robertstrauss/laser-projector/blender-CAD-modeling/laser-diffusion-raytracing/focal-cone-cloud-tight-no-denoise.png

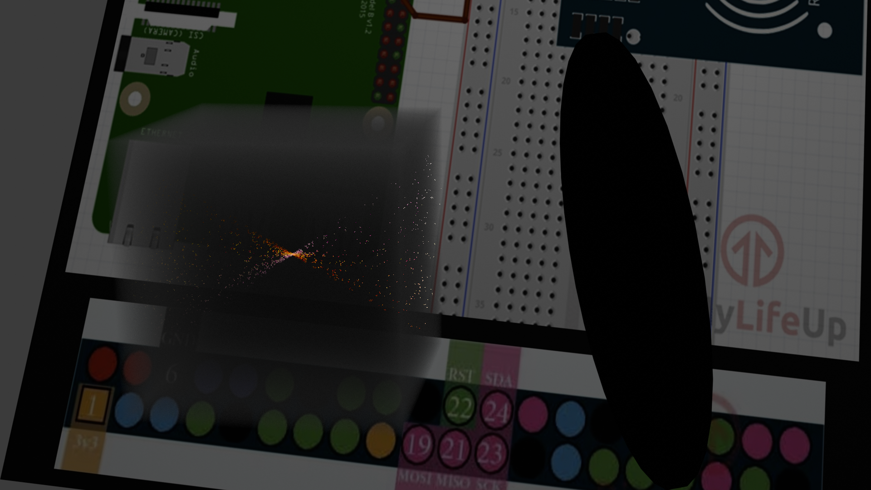
blender-CAD-modeling/laser-diffusion-raytracing/focal-cone-cloud-tight-no-denoise.png
