robertstrauss/laser-projector/blender-CAD-modeling/laser-diffusion-raytracing/focal-cone-cloud.png

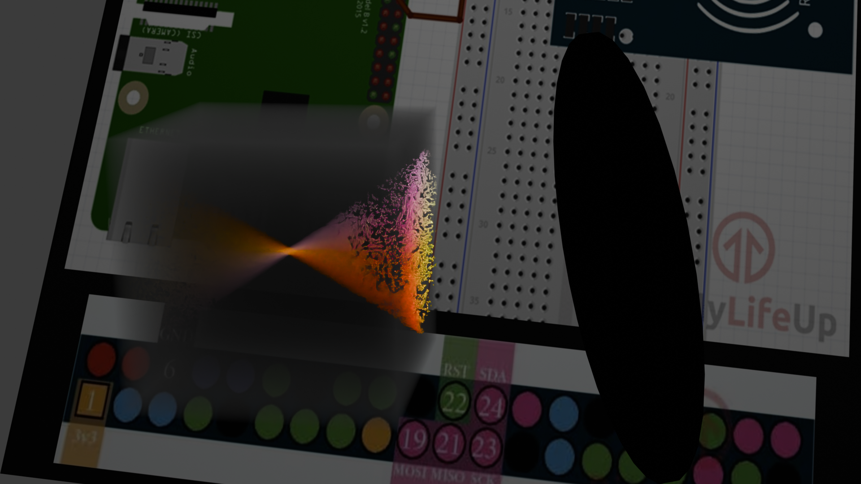
blender-CAD-modeling/laser-diffusion-raytracing/focal-cone-cloud.png
